sweetlilmre/tapuino/layout/eagle/TapuinoMini/1.01/TapuinoMiniDouble_bottom.png

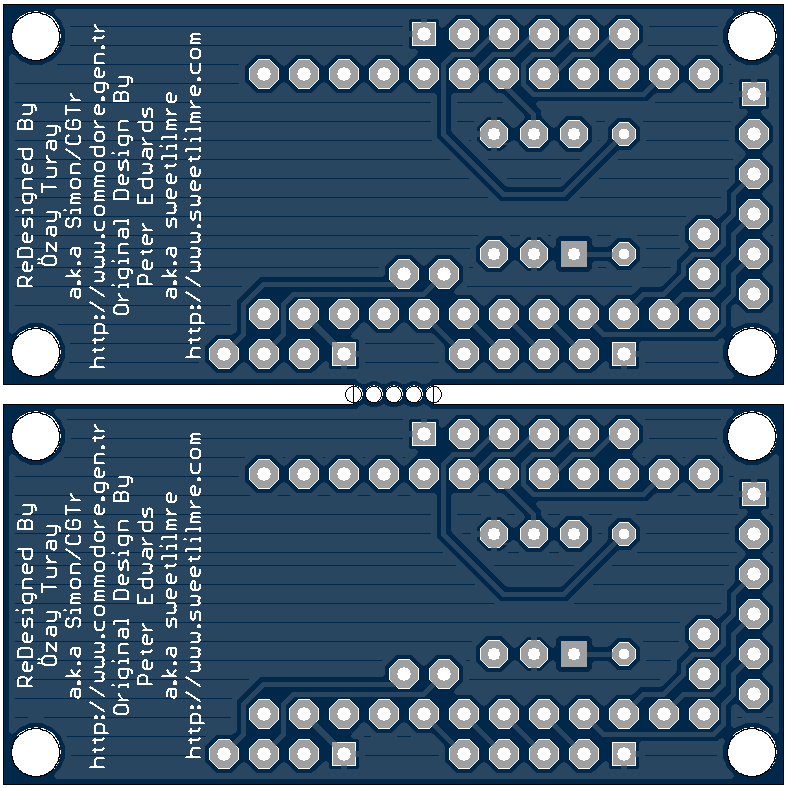
layout/eagle/TapuinoMini/1.01/TapuinoMiniDouble_bottom.png
