sweetlilmre/tapuino/layout/eagle/TapuinoMini/1.01/TapuinoMiniDouble_top.png

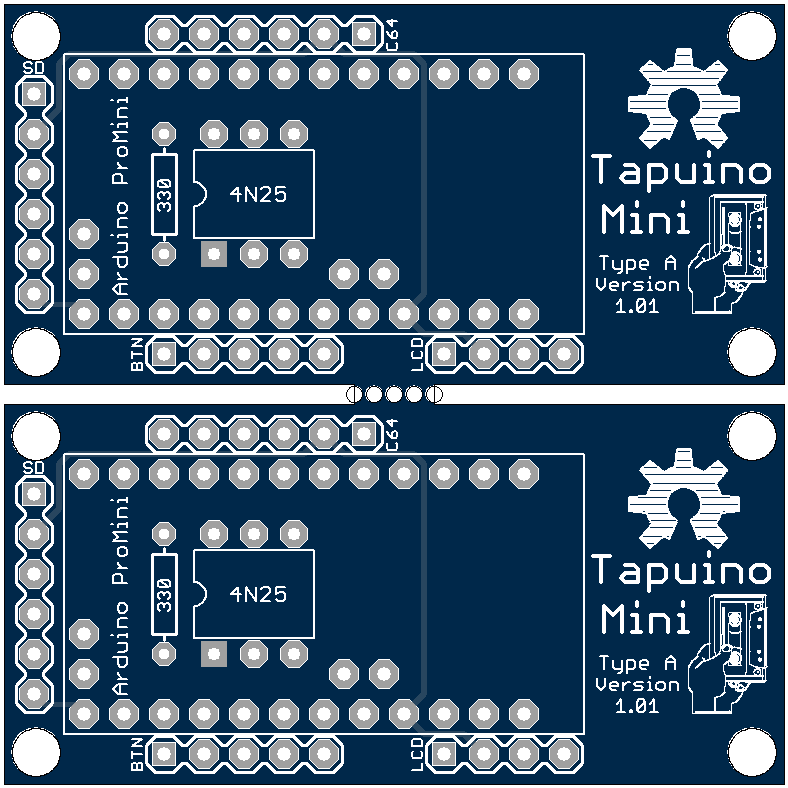
layout/eagle/TapuinoMini/1.01/TapuinoMiniDouble_top.png
