sweetlilmre/tapuino/layout/eagle/TapuinoMini/1.02/TapuinoMiniDouble_bottom.png

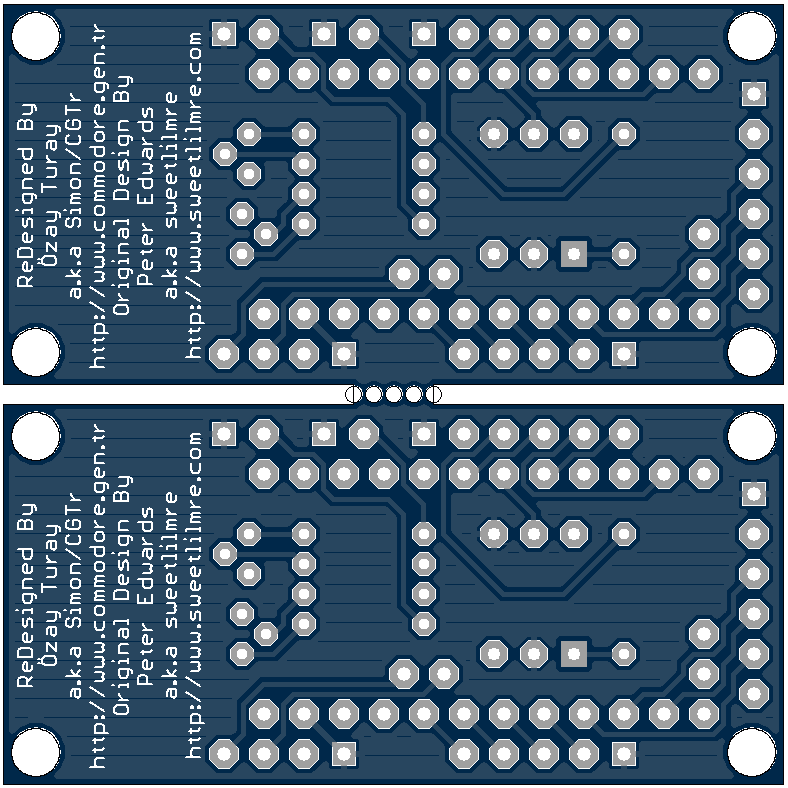
layout/eagle/TapuinoMini/1.02/TapuinoMiniDouble_bottom.png
