sweetlilmre/tapuino/layout/eagle/TapuinoMini/1.02/TapuinoMiniDouble_top.png

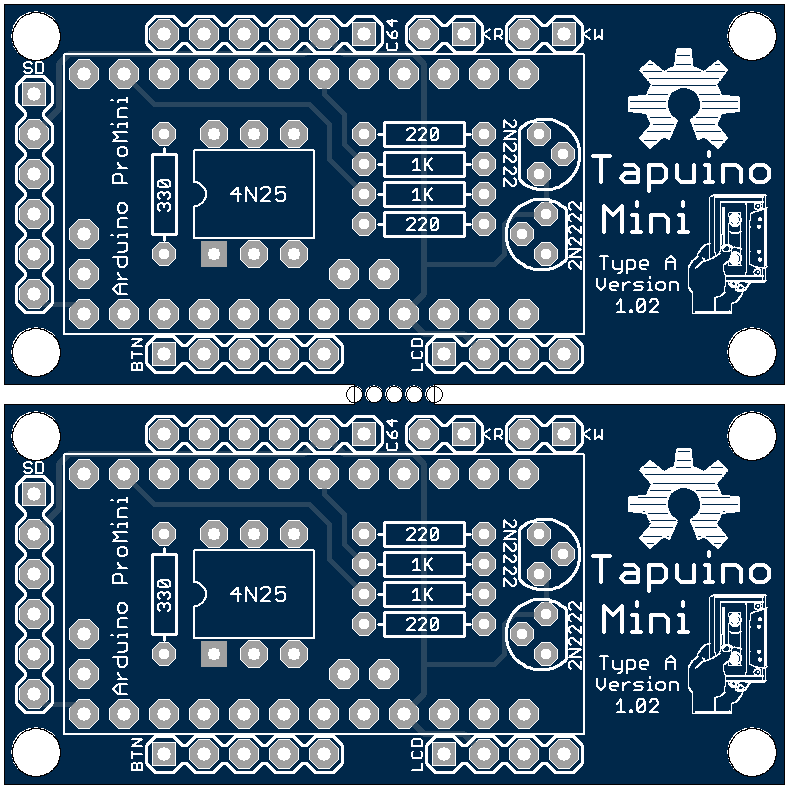
layout/eagle/TapuinoMini/1.02/TapuinoMiniDouble_top.png
