sweetlilmre/tapuino/layout/tapuino-main-r2.png

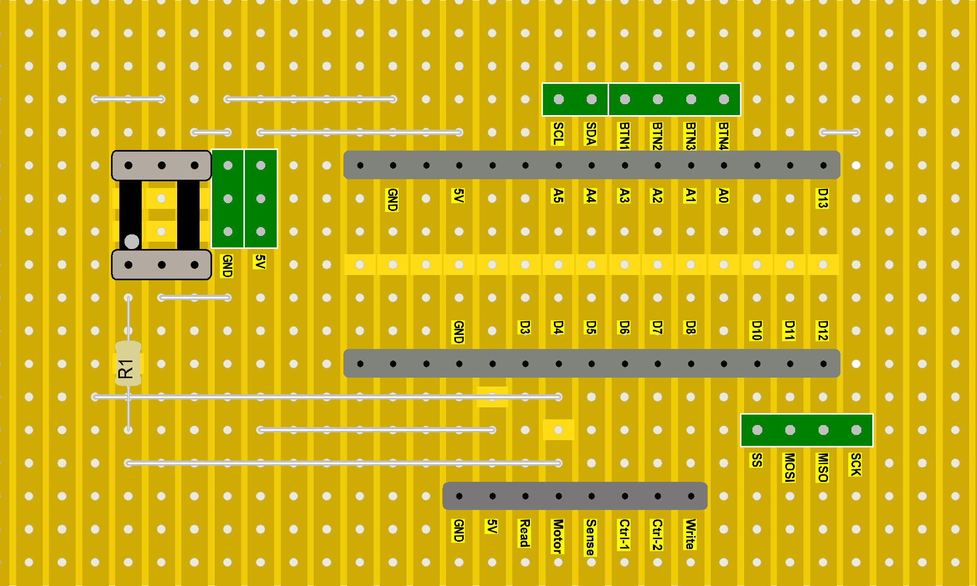
layout/tapuino-main-r2.png
