sweetlilmre/tapuino/layout/tapuino-mux-board-r1.png

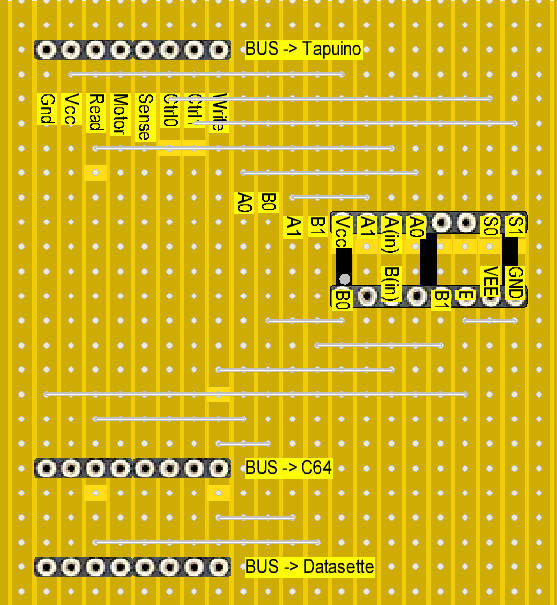
layout/tapuino-mux-board-r1.png
