sweetlilmre/tapuino/layout/tapuino-mux-board-r2-bottom.png

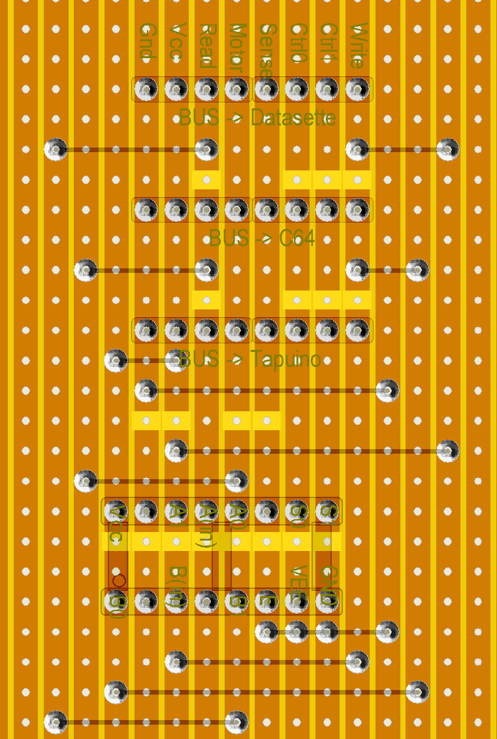
layout/tapuino-mux-board-r2-bottom.png
