sweetlilmre/tapuino/layout/tapuino_bb-r2.png

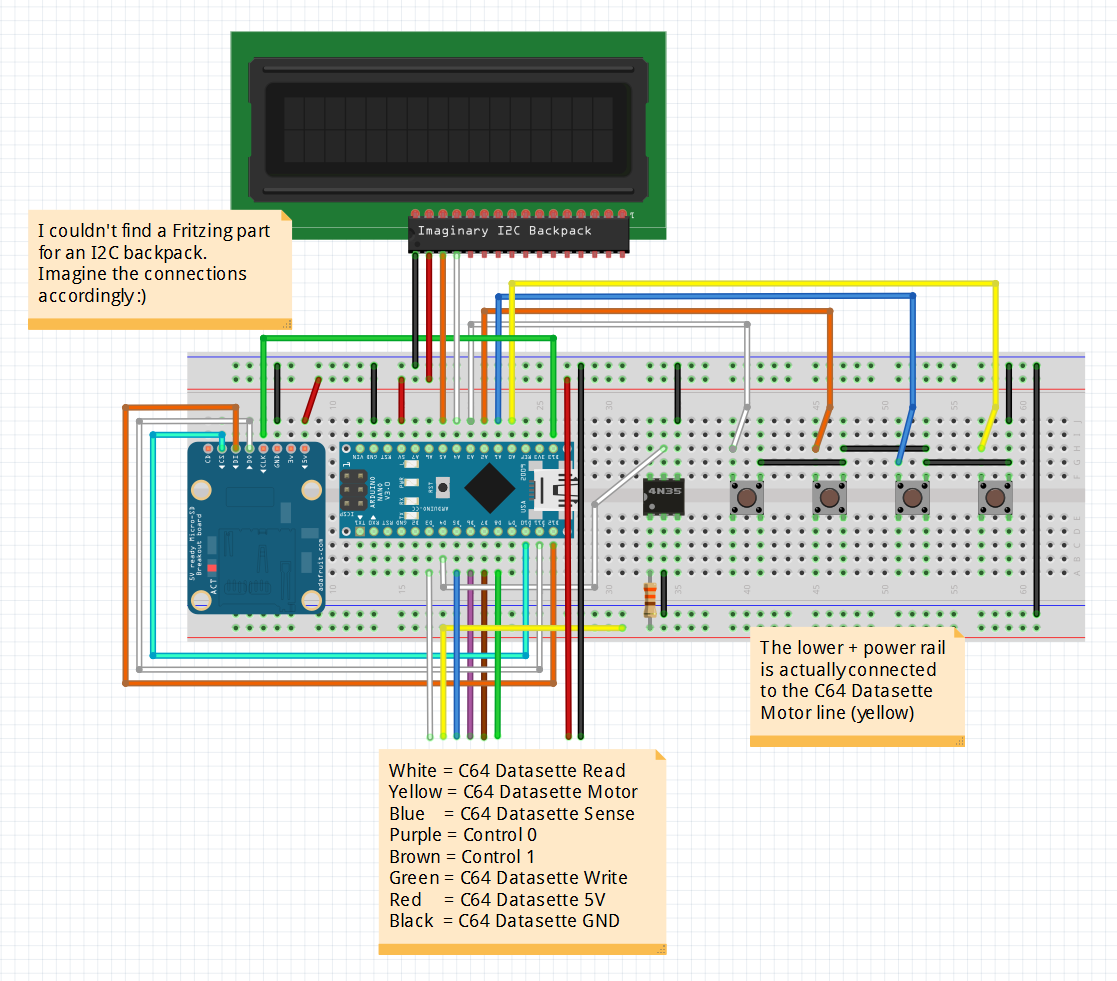
layout/tapuino_bb-r2.png
