sweetlilmre/tapuino/layout/tapuino_bb.png

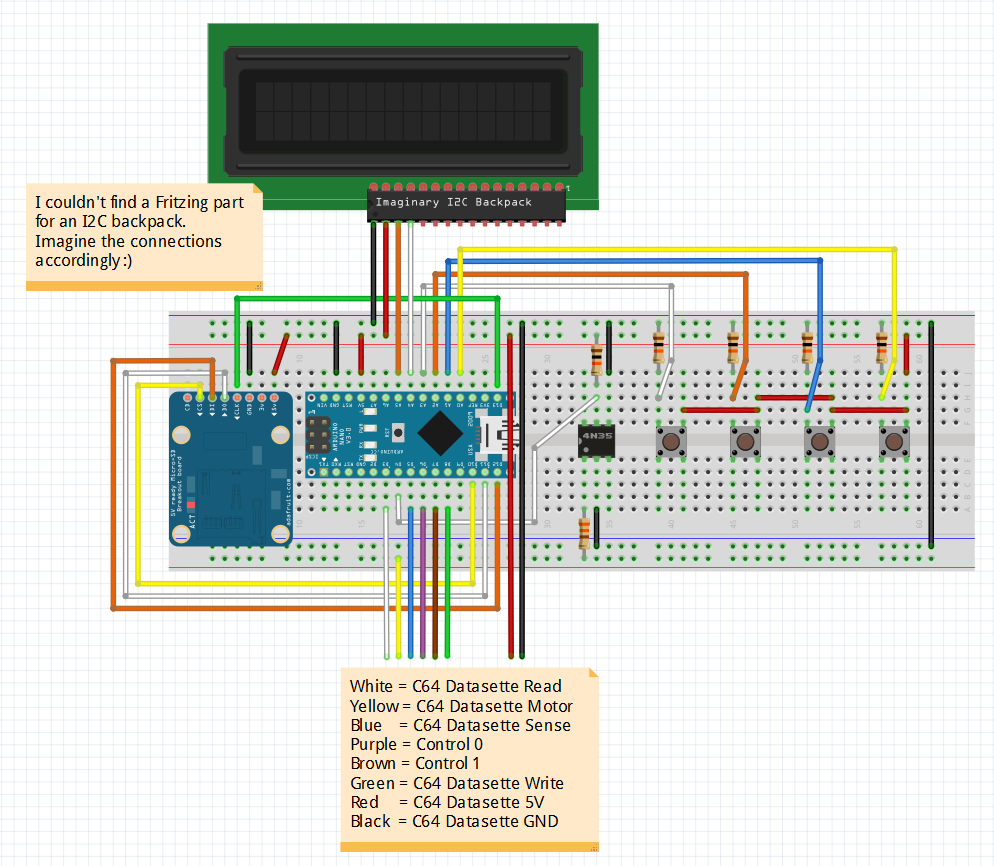
layout/tapuino_bb.png
