sweetlilmre/tapuino/layout/Vero-bottom.png

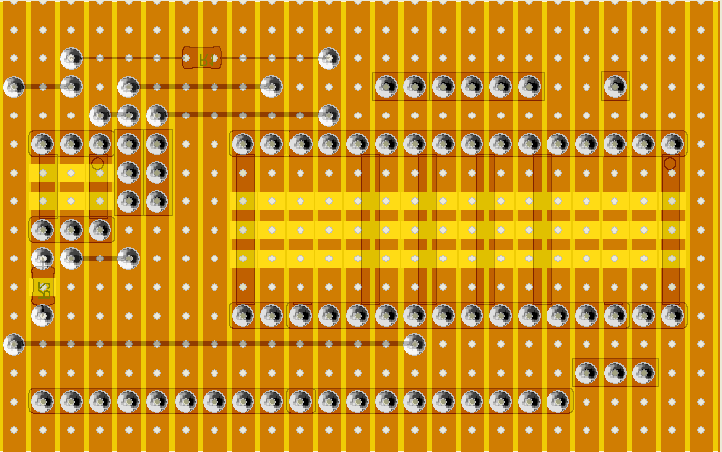
layout/Vero-bottom.png
