sweetlilmre/tapuino/layout/Vero-button-bottom-r2.png

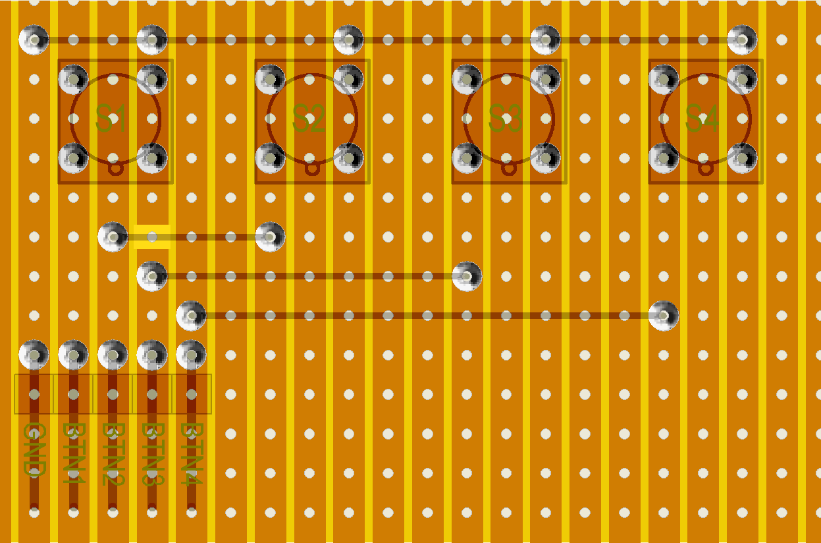
layout/Vero-button-bottom-r2.png
