sweetlilmre/tapuino/layout/Vero-button-bottom.png

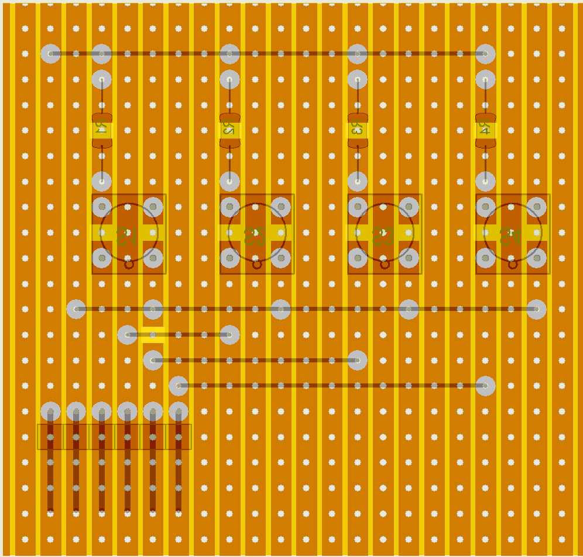
layout/Vero-button-bottom.png
