sweetlilmre/tapuino/layout/Vero-button-top-r2.png

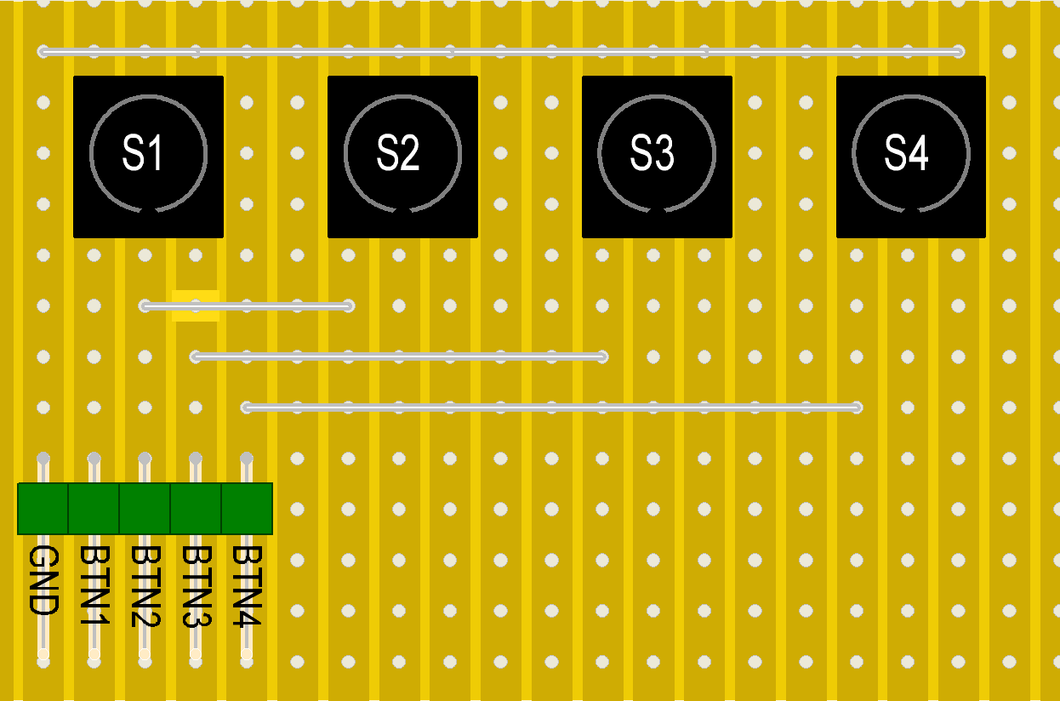
layout/Vero-button-top-r2.png
