sweetlilmre/tapuino/layout/Vero-button-top.png

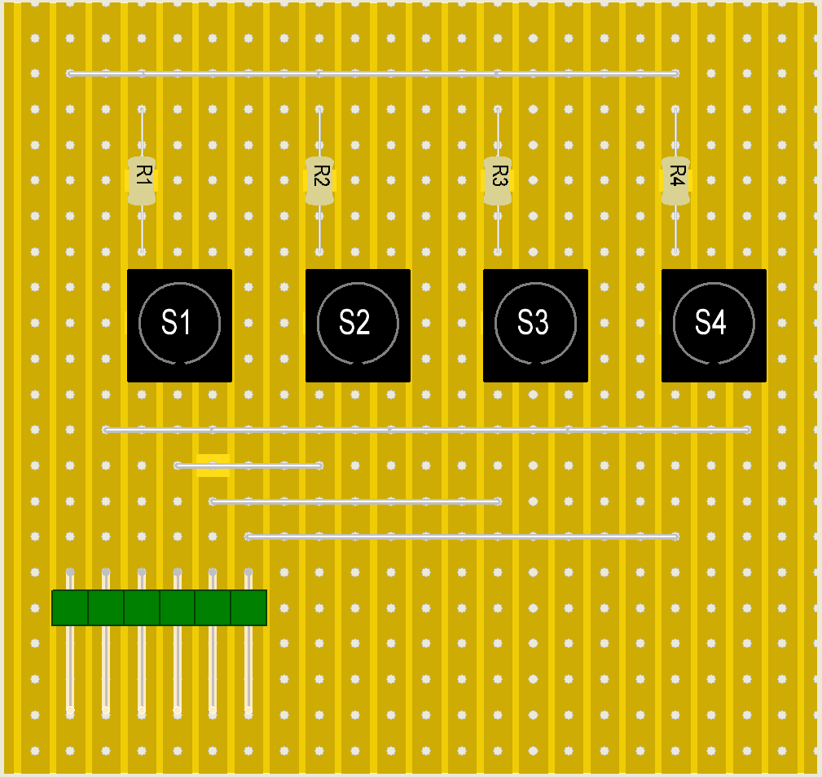
layout/Vero-button-top.png
