sweetlilmre/tapuino/layout/Vero-top.png

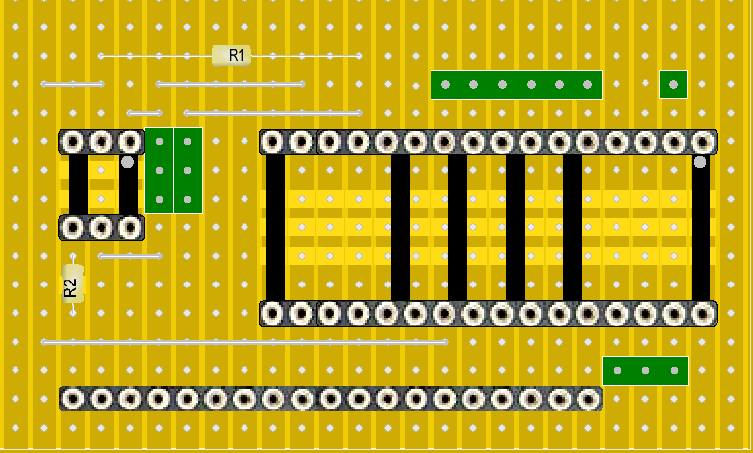
layout/Vero-top.png
