sweetlilmre/tapuino/main.c

/*
 * Tapuino.c
 *
 * Created: 2014/10/04 04:31:40 PM
 *  Author: sweetlilmre
 */ 

#ifndef ARDUINO

#include <avr/io.h>
#include "tapuino.h"

int main(void)
{
    while(1)
    {
		tapuino_run();
        //TODO:: Please write your application code 
    }
}

#endif
