sweetlilmre/tapuino/memstrings.h

#ifndef _MEMSTRINGS_H
#define _MEMSTRINGS_H

#include <avr/pgmspace.h>

extern const char S_DEFAULT_RECORD_DIR[];
extern const char S_NAME_PATTERN[];
extern const char S_RECORDING[];
extern const char S_SELECT_RECORD_MODE[];
extern const char S_REC_MODE_MANUAL[];
extern const char S_REC_MODE_AUTO[];
extern const char S_ENTER_FILENAME[];
extern const char S_FILENAME_CHARS[];

extern const char S_STARTINGINIT[];
extern const char S_INITI2COK[];
extern const char S_INIT[];
extern const char S_INIT_FAILED[];
extern const char S_INIT_OK[];
extern const char S_NO_FILES_FOUND[];
extern const char S_SELECT_FILE[];
extern const char S_SELECT_MODE[];
extern const char S_MODE_PLAY[];
extern const char S_MODE_RECORD[];
extern const char S_READY_RECORD[];
extern const char S_PRESS_START[];

extern const char S_MODE_OPTIONS[];
extern const char S_OPTION_SIGNAL[];
extern const char S_OPTION_KEY_REPEAT[];
extern const char S_OPTION_TICKER_SPEED[];
extern const char S_OPTION_TICKER_HOLD[];
extern const char S_OPTION_REC_FINALIZE[];
extern const char S_OPTION_REC_AUTO_FINALIZE[];


extern const char S_MKDIR_FAILED[];
extern const char S_CHDIR_FAILED[];
extern const char S_READ_FAILED[];
extern const char S_OPEN_FAILED[];
extern const char S_INVALID_TAP[];
extern const char S_INVALID_SIZE[];
extern const char S_LOADING[];
extern const char S_OPERATION_COMPLETE[];
extern const char S_OPERATION_ABORTED[];


extern const char S_OPTION_MACHINE_TYPE[];
extern const char S_C64[];
extern const char S_C16[];
extern const char S_VIC[];

extern const char S_OPTION_VIDEO_MODE[];
extern const char S_PAL[];
extern const char S_NTSC[];

extern const char S_VERSION_PATTERN[];

#endif
